mk20661/SDV_Group_Assessignment/unity/inmodelT/inmodelT/Assets/firework/d5e9ae9cdaf2aa72afef1052491f279b.jpeg

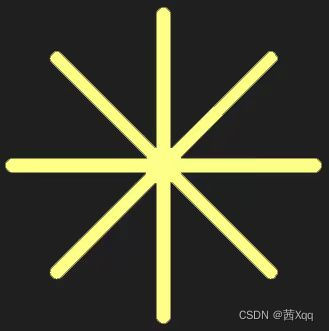
unity/inmodelT/inmodelT/Assets/firework/d5e9ae9cdaf2aa72afef1052491f279b.jpeg
